espcaa/mp3-player/assets/20-06-26_02.jpg

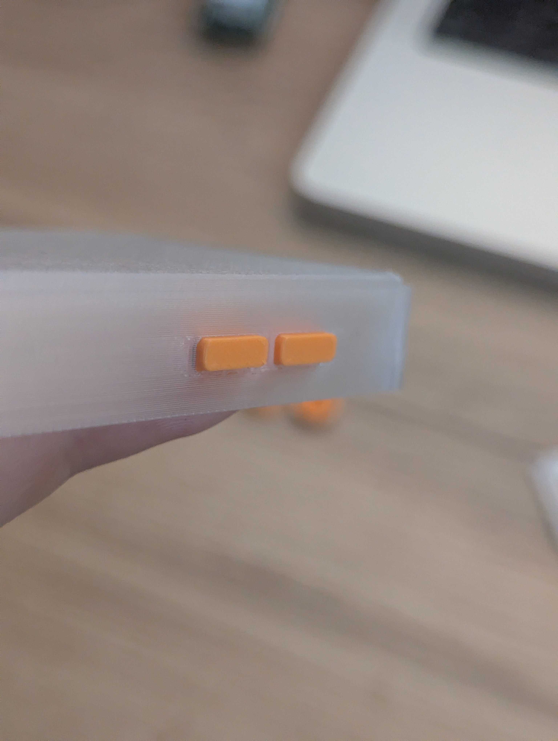
assets/20-06-26_02.jpg
