espcaa/mp3-player/misc/ui_texture.png

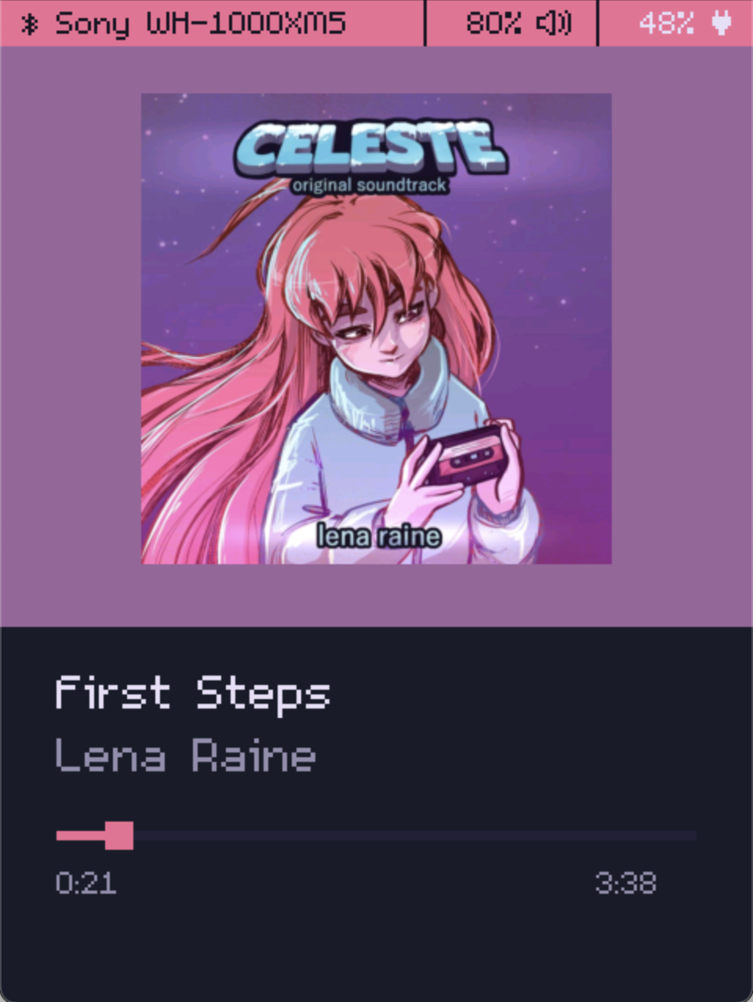
misc/ui_texture.png
