espcaa/mp3-player/src/firmware/src/hal_pico/st7701s.c

#include "st7701s.h"
#include "pico/stdlib.h"

#define PIN_RST 11
#define PIN_CS 13
#define PIN_SCK 14
#define PIN_SDA 15

#define CMD_DELAY 0xFE // table sentinel: next byte = delay in ms

// ER-TFT028A5-4 init (BuyDisplay), RGB565 (0x3A=0x55). rows: cmd, nparams, ...
static const uint8_t INIT[] = {
    0xFF, 5, 0x77, 0x01, 0x00, 0x00, 0x13,
    0xEF, 1, 0x08,
    0xFF, 5, 0x77, 0x01, 0x00, 0x00, 0x10,
    0xC0, 2, 0x4F, 0x00,
    0xC1, 2, 0x10, 0x0C,
    0xC2, 2, 0x01, 0x14,
    0xCC, 1, 0x10,
    0xB0, 16, 0x0A, 0x18, 0x1E, 0x12, 0x16, 0x0C, 0x0E, 0x0D, 0x0C, 0x29, 0x06,
    0x14, 0x13, 0x29, 0x33, 0x1C,
    0xB1, 16, 0x0A, 0x19, 0x21, 0x0A, 0x0C, 0x00, 0x0C, 0x03, 0x03, 0x23, 0x01,
    0x0E, 0x0C, 0x27, 0x2B, 0x1C,
    0xFF, 5, 0x77, 0x01, 0x00, 0x00, 0x11,
    0xB0, 1, 0x5D,
    0xB1, 1, 0x4F,
    0xB2, 1, 0x00,
    0xB3, 1, 0x80,
    0xB5, 1, 0x0C,
    0xB7, 1, 0x85,
    0xB8, 1, 0x20,
    0xC1, 1, 0x78,
    0xC2, 1, 0x78,
    0xD0, 1, 0x88,
    0xE0, 3, 0x00, 0x00, 0x02,
    0xE1, 11, 0x06, 0xA0, 0x08, 0xA0, 0x05, 0xA0, 0x07, 0xA0, 0x00, 0x44, 0x44,
    0xE2, 12, 0x20, 0x20, 0x44, 0x44, 0x96, 0xA0, 0x00, 0x00, 0x96, 0xA0, 0x00,
    0x00,
    0xE3, 4, 0x00, 0x00, 0x22, 0x22,
    0xE4, 2, 0x44, 0x44,
    0xE5, 16, 0x0D, 0x91, 0x0A, 0xA0, 0x0F, 0x93, 0x0A, 0xA0, 0x09, 0x8D, 0x0A,
    0xA0, 0x0B, 0x8F, 0x0A, 0xA0,
    0xE6, 4, 0x00, 0x00, 0x22, 0x22,
    0xE7, 2, 0x44, 0x44,
    0xE8, 16, 0x0C, 0x90, 0x0A, 0xA0, 0x0E, 0x92, 0x0A, 0xA0, 0x08, 0x8C, 0x0A,
    0xA0, 0x0A, 0x8E, 0x0A, 0xA0,
    0xE9, 2, 0x36, 0x00,
    0xEB, 7, 0x00, 0x01, 0xE4, 0xE4, 0x44, 0x88, 0x40,
    0xED, 16, 0xFF, 0x45, 0x67, 0xFA, 0x01, 0x2B, 0xCF, 0xFF, 0xFF, 0xFC, 0xB2,
    0x10, 0xAF, 0x76, 0x54, 0xFF,
    0xEF, 6, 0x10, 0x0D, 0x04, 0x08, 0x3F, 0x1F,
    0x3A, 1, 0x55, // COLMOD: RGB565 (was 0x66 = RGB666)
    0x11, 0,       // sleep out
    CMD_DELAY, 1, 120,
    0x36, 1, 0x00,
    0x35, 1, 0x00,
    0x29, 0, // display on
};

static void spi_send(uint8_t b) {
  for (int n = 0; n < 8; n++) {
    gpio_put(PIN_SCK, 0);
    gpio_put(PIN_SDA, (b & 0x80) ? 1 : 0);
    b <<= 1;
    sleep_us(1);
    gpio_put(PIN_SCK, 1);
    sleep_us(1);
  }
}

// 9-bit word: leading bit dc (0=command, 1=data), then the byte
static void spi_word(bool dc, uint8_t v) {
  gpio_put(PIN_CS, 0);
  gpio_put(PIN_SCK, 0);
  gpio_put(PIN_SDA, dc);
  sleep_us(1);
  gpio_put(PIN_SCK, 1);
  sleep_us(1);
  spi_send(v);
  gpio_put(PIN_CS, 1);
}

void st7701s_init(void) {
  gpio_init(PIN_RST);
  gpio_init(PIN_CS);
  gpio_init(PIN_SCK);
  gpio_init(PIN_SDA);
  gpio_set_dir(PIN_RST, GPIO_OUT);
  gpio_set_dir(PIN_CS, GPIO_OUT);
  gpio_set_dir(PIN_SCK, GPIO_OUT);
  gpio_set_dir(PIN_SDA, GPIO_OUT);
  gpio_put(PIN_CS, 1);

  gpio_put(PIN_RST, 1);
  sleep_ms(10);
  gpio_put(PIN_RST, 0);
  sleep_ms(10);
  gpio_put(PIN_RST, 1);
  sleep_ms(120);

  for (size_t i = 0; i < sizeof(INIT);) {
    uint8_t cmd = INIT[i++];
    uint8_t n = INIT[i++];
    if (cmd == CMD_DELAY) {
      sleep_ms(INIT[i]);
      i += n;
      continue;
    }
    spi_word(false, cmd);
    for (uint8_t k = 0; k < n; k++)
      spi_word(true, INIT[i++]);
  }
}
