espcaa/mp3-player/src/firmware/src/ui/components/now_playing_bar.h

#ifndef NOW_PLAYING_BAR_H
#define NOW_PLAYING_BAR_H

#include "../widget.h"

widget_t *now_playing_bar_create(int16_t x, int16_t y, int16_t width,
                                 int16_t height);

#endif
